Bbethanyy/Projecte_MiSE/clock.h

/*
 * clock.h
 *
 *  Created on: 23 abr. 2024
 *      Author: USUARIO
 */

#ifndef LIBRERIAS_ROBOT_CLOCK_H_
#define LIBRERIAS_ROBOT_CLOCK_H_

void init_clocks(void);

#endif /* LIBRERIAS_ROBOT_CLOCK_H_ */
